turingbirds/motionsensor/sims/motion_sensor_v9.asc

C1: cap; 470n
C2: cap; 2n2
C3: cap; 2n2
C4: cap; 22n
C5: cap; 470n
C6: cap; 120n
C7: cap; 47n
C8: cap; 10µ
C9: cap; 47n
C10: cap; 82n
C12: cap; 1.8n
D1: LED; NSCW100
D2: LED; NSCW100
D3: diode
R1: res; 100
R2: res; 100k
R3: res; 10k
R4: res; 100k
R5: res; 1k
R6: res; 100
R7: res; 100k
R8: res; 10k
R9: res; 1k
R11: res; 100k
R14: res; 10k
R17: res; 1k5
R18: res; 1k
R25: res; 10
R26: res; 150
R27: res; 50k
R28: res; 10k
R29: res; 10k
U1: UniversalOpamp2
U2: UniversalOpamp2
U3: UniversalOpamp2
U4: UniversalOpamp2
U5: UniversalOpamp2
U6: UniversalOpamp2
V1: voltage; SINE(0 30e-6 100 3 0 0 50); AC 0.0005
V2: voltage; 5
V3: voltage; 5
V4: voltage; 5
V5: voltage; 5
V6: voltage; 5
V7: voltage; 5
V8: voltage; 5
V9: voltage; 5
V10: voltage; 300m
V11: voltage; 5
V12: voltage; 5
V13: voltage; 5
V19: voltage; SINE(0 1e-3 10 0.5 0 0 10); AC 0.0005
V20: voltage; 5
V21: voltage; 3.3
Named nets: 0
;tran 0 10 0 startup
.ac oct 100 0.1 10000
to ADC
from ADC REF pin
min resistance 150R
